SomeLucky1/GCLegoPCB/Accessories/Images/ToFnLED-RGBW.png

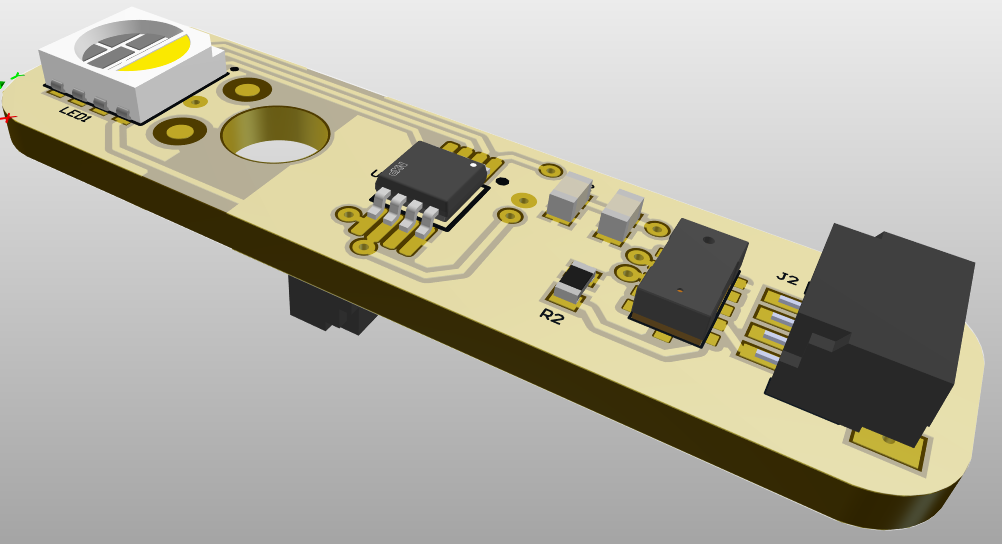
Accessories/Images/ToFnLED-RGBW.png
