SomeLucky1/GCLegoPCB/Case/Images/LegoPCBCase-Populated-Top-Molex.png

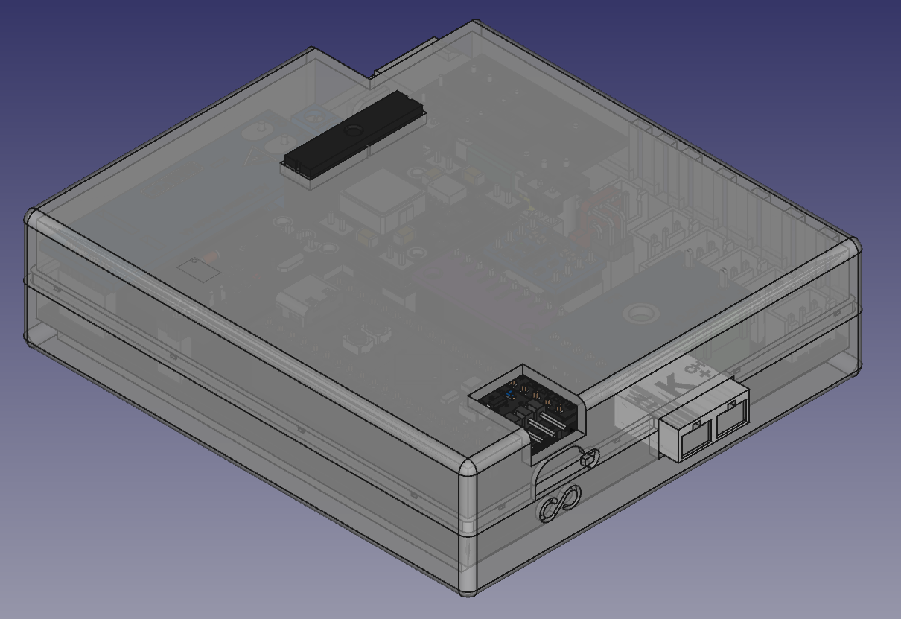
Case/Images/LegoPCBCase-Populated-Top-Molex.png
