SomeLucky1/GCLegoPCB/PCB/Images/LegoPCB-Populated_Render.png

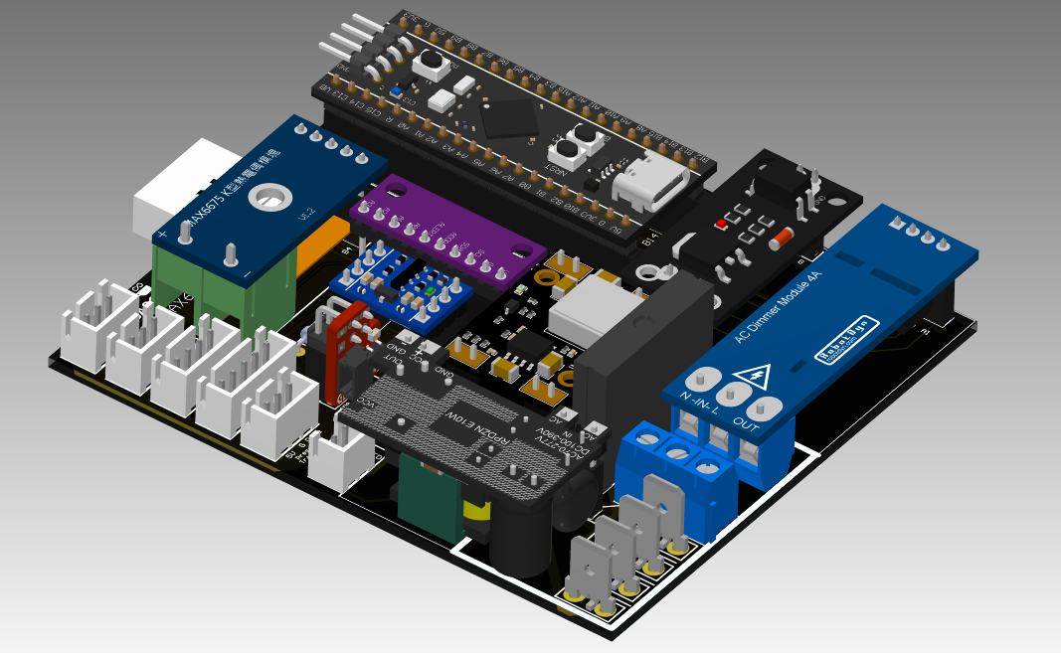
PCB/Images/LegoPCB-Populated_Render.png
