SomeLucky1/GCLegoPCB/PCB/Molex/Images/Lego-PCB-Molex-Populated-Render.png

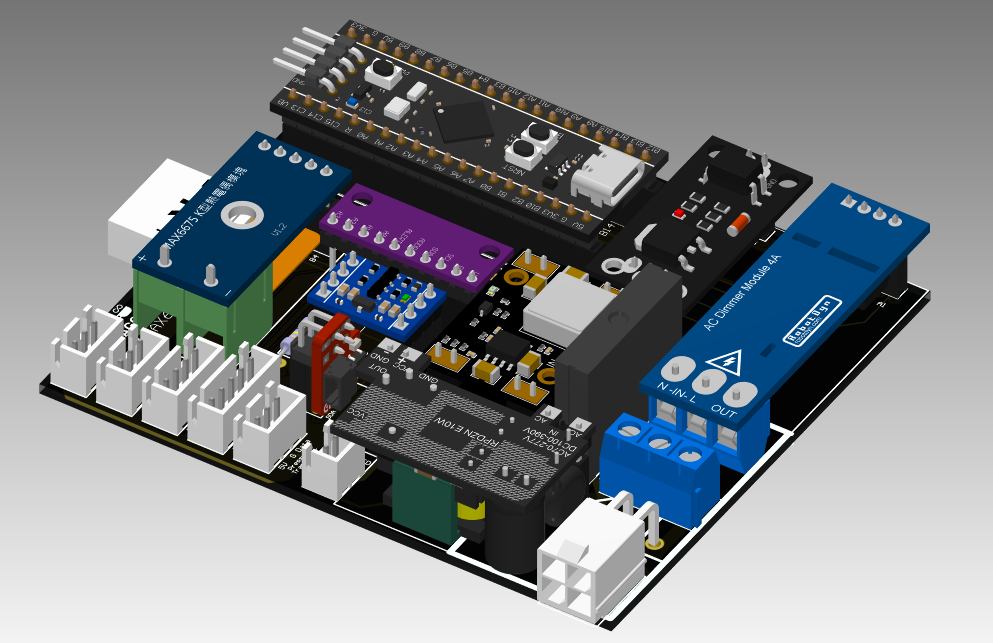
PCB/Molex/Images/Lego-PCB-Molex-Populated-Render.png
