SomeLucky1/GCLegoPCB/PCB/Molex/Images/Lego-PCB-Molex-Top-Populated.png

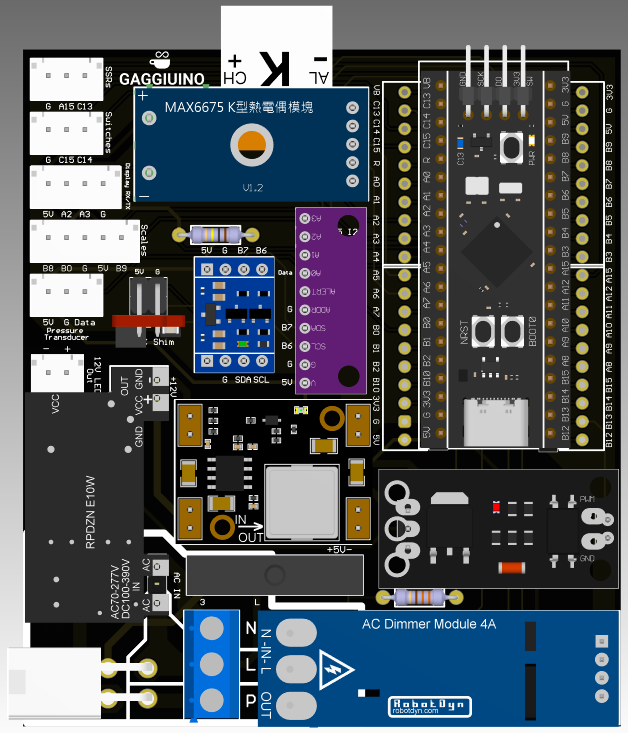
PCB/Molex/Images/Lego-PCB-Molex-Top-Populated.png
